UCDBioe/Bioe3090_Incubator/Diagrams/LTSpice_schematics/Images/PullDown_drvSig.png

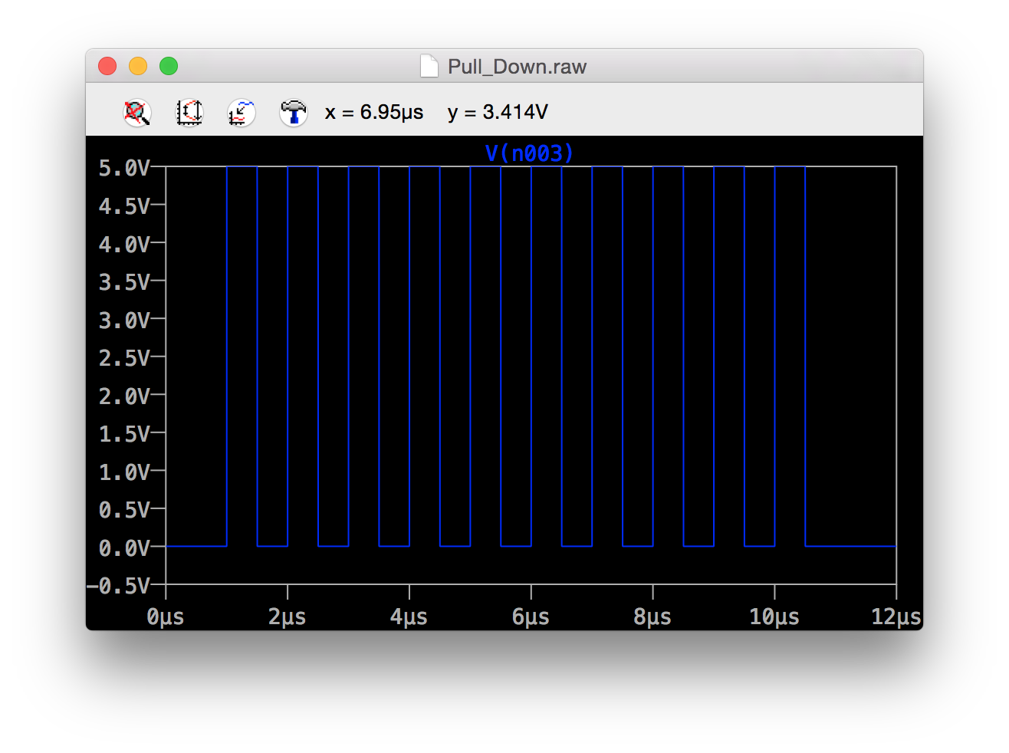
Diagrams/LTSpice_schematics/Images/PullDown_drvSig.png
