UCDBioe/Bioe3090_Incubator/Diagrams/LTSpice_schematics/Pull_Down.asc

C1: cap; 1p
PullDown: res; 10K
R2: res; 100Meg
S1: sw; MYSW
V1: voltage; PULSE(0 5 1u .001u .001u .5u 1u 10)
V2: voltage; 5
Named nets: 0
.tran 0 12u 0
.model MYSW SW(Ron=1 Roff=1Meg Vt=0.5 Vh=-0.4)
ARDUINO PIN
