UCDBioe/Bioe3090_Incubator/Diagrams/LTSpice_schematics/LTSpice_Heater_.asc

C1: cap; 1m
D1: schottky
D2: LED
M1: nmos; BSC031N06NS3
R1: res; 3.3Meg
R2: res; 2.2Meg
R3: res; 390
R4: res; 22K
R5: res; 10
R6: res; 100Meg
V1: voltage; 12
V2: voltage; PULSE(0 5 0 10u 10u 500u 1020u)
Named nets: 0
.tran 0 .2s 0 1u
Heater
Ardu Pin 6
Decoupling
Capacitor
