UCDBioe/Bioe3090_Incubator/Diagrams/Draft1.asc

R1: res; 10
R2: res; 5
U1: opamp
V1: voltage; 5
Named nets: 0
.tran 0 4ms 0
.lib opamp.sub
